GameOver94/open-AutopilotPanel/3D printing files/Knob 8 Slot.stl

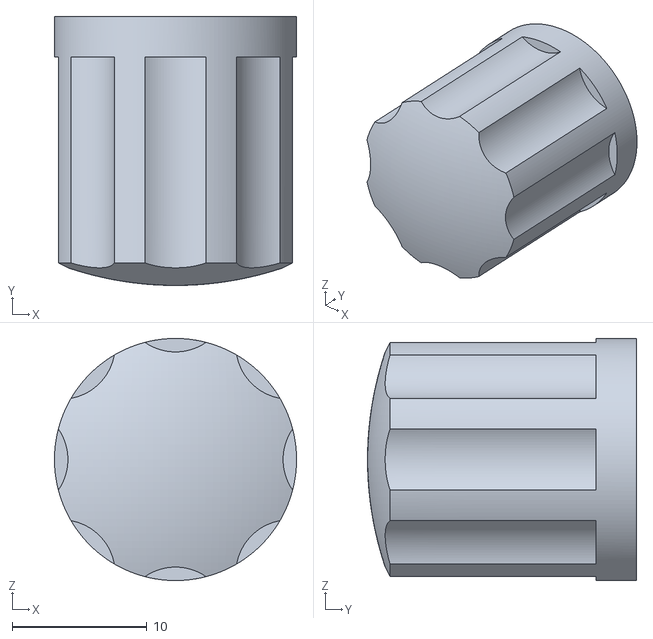
[picture p17: CAD file, 2021-03-19]
3D printing files/Knob 8 Slot.stl
18.0 x 20.0 x 18.0
