GameOver94/open-AutopilotPanel/3D printing files/Button_Autopilot v12_Körper5_Button.stl

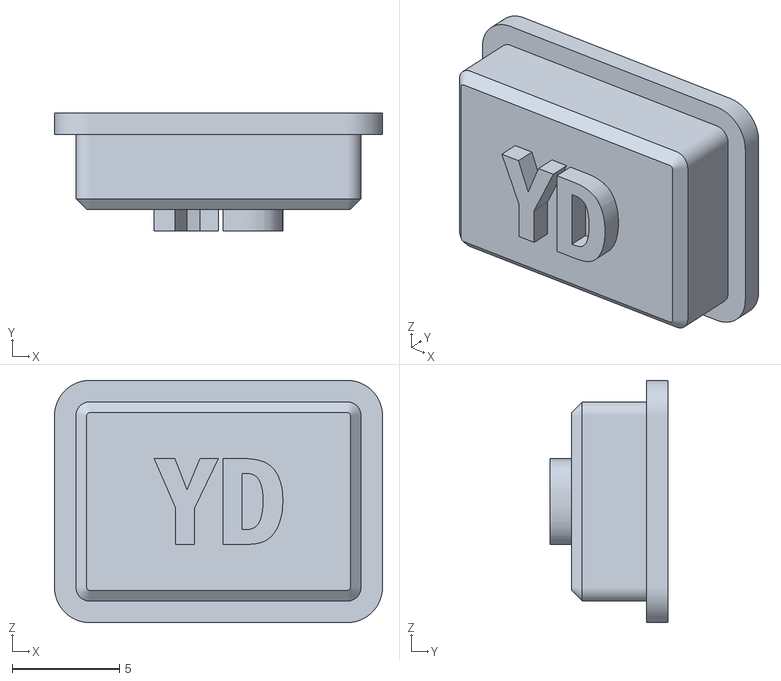
[picture p18: CAD file, 2021-03-19]
3D printing files/Button_Autopilot v12_Körper5_Button.stl
15.3 x 5.50 x 11.3
